audrentis/OSTKL/H88/7U ANSI Plate.dxf

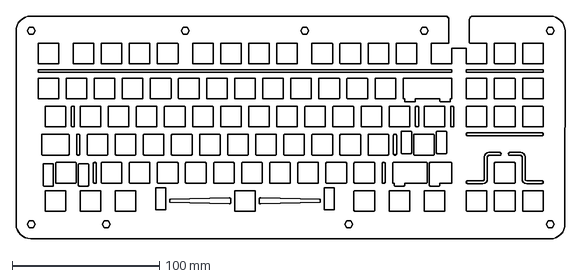
[picture p19: CAD file, 2021-01-26]
H88/7U ANSI Plate.dxf
372.4 x 151.0 mm
